kajusK/Pneumobil/fw/sources/app/hmi/state.c

/*
    BUT pneumobil - Copyright (C) 2018 Jakub Kaderka.

    This file is part of BUT pneumobil.

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
    You should have received a copy of the GNU General Public License
    along with this program.  If not, see <http://www.gnu.org/licenses/>.
*/

/**
 * @file    hmi/state.c
 * @brief   Collecting data from various modules to get car state
 *
 * @addtogroup app-hmi
 * @{
 */

#include <string.h>
#include <modules/log.h>
#include <modules/comm/comm.h>
#include <utils/time.h>
#include <utils/assert.h>

#include "logger.h"
#include "state.h"

/** Time from last module seen time to consider it online */
#define STATE_CONSIDER_ONLINE_MS 5000

static uint32_t statei_race_start_ts;
static state_t statei_state;
static state_pneu_t * const statei_pneu = &statei_state.pneu;
static state_car_t * const statei_car = &statei_state.car;
static state_psu_t * const statei_psu = &statei_state.psu;

static void Statei_SetNodeOnline(state_node_t *module)
{
    ASSERT_NOT(module == NULL);

    if ((millis() - module->_seen) > STATE_CONSIDER_ONLINE_MS) {
        module->online = false;
    } else {
        module->online = true;
    }
}

void State_UpdateCarState(uint16_t speed_dms, uint16_t speed_avg_dms,
        uint16_t distance_m, race_mode_t mode)
{
    statei_car->speed_kmh = speed_dms*0.36;
    statei_car->speed_avg_kmh = speed_avg_dms*0.36;
    statei_car->distance_m = distance_m;
    statei_car->mode = mode;

    if (statei_car->speed_kmh > statei_car->speed_max_kmh) {
        statei_car->speed_max_kmh = statei_car->speed_kmh;
    }
}

void State_UpdateCarIoState(valve_state_t front1, valve_state_t front2,
        valve_state_t back1, valve_state_t back2, bool endstop_front,
        bool endstop_back, bool throttle, bool brake, bool horn, bool shifting,
        uint8_t gear)
{
    statei_pneu->valve_front1 = front1;
    statei_pneu->valve_front2 = front2;
    statei_pneu->valve_back1 = back1;
    statei_pneu->valve_back2 = back2;
    statei_pneu->endstop_front = endstop_front;
    statei_pneu->endstop_back = endstop_back;
    statei_car->throttle = throttle;
    statei_car->brake = brake;
    statei_car->horn = horn;
    statei_car->shifting = shifting;
    statei_car->gear = gear;
}

void State_UpdatePneuState(uint16_t press1_kpa, uint16_t press2_kpa,
        uint16_t press3_kpa, uint8_t piston_pos_pct)
{
    statei_pneu->press1_kpa = press1_kpa;
    statei_pneu->press2_kpa = press2_kpa;
    statei_pneu->press3_kpa = press3_kpa;
    statei_pneu->piston_pct = piston_pos_pct;
}

void State_UpdateBattery(uint16_t bat1_mv, uint16_t bat2_mv, uint16_t cur_ma,
        uint8_t charge_pct)
{
    statei_psu->battery.bat1_mv = bat1_mv;
    statei_psu->battery.bat2_mv = bat2_mv;
    statei_psu->battery.cur_ma = cur_ma;
    statei_psu->battery.charge_pct = charge_pct;
}

void State_UpdatePSUCurrent(uint16_t cur5v_ma, uint16_t cur12v_ma,
        uint16_t cur24v_ma)
{
    statei_psu->psu5_ma = cur5v_ma;
    statei_psu->psu12_ma = cur12v_ma;
    statei_psu->psu24_ma = cur24v_ma;
}

void State_UpdatePSUVoltage(uint16_t volt5_mv, uint16_t volt12_mv,
        uint16_t volt24_mv)
{
    statei_psu->psu5_mv = volt5_mv;
    statei_psu->psu12_mv = volt12_mv;
    statei_psu->psu24_mv = volt24_mv;
}

void State_UpdateNode(comm_node_t node, uint16_t uptime_s, int8_t temp_c,
        uint16_t core_mv)
{
    state_node_t *node_var;

    switch (node) {
        case COMM_NODE_PSU:
            node_var = &statei_state.node.psu;
            break;
        case COMM_NODE_ECU:
            node_var = &statei_state.node.ecu;
            break;
        case COMM_NODE_SDU:
            node_var = &statei_state.node.sdu;
            break;
        case COMM_NODE_DEBUG:
            node_var = &statei_state.node.dbg;
            break;
        case COMM_NODE_HMI:
            Log_Error(LOG_SOURCE_APP,
                    "Received state of HMI that was not sent by HMI");
            return;
            break;
        default:
            Log_Error(LOG_SOURCE_APP, "Received state for unknown module %d",
                    node);
            return;
            break;
    }

    node_var->uptime_s = uptime_s;
    node_var->temp_c = temp_c;
    node_var->core_mv = core_mv;
    node_var->_seen = millis();
}

state_t *State_Get(void)
{
    Statei_SetNodeOnline(&statei_state.node.ecu);
    Statei_SetNodeOnline(&statei_state.node.psu);
    Statei_SetNodeOnline(&statei_state.node.sdu);
    Statei_SetNodeOnline(&statei_state.node.dbg);

    //TODO
    statei_state.node.hmi.online = true;
    statei_state.node.hmi.core_mv = 0;
    statei_state.node.hmi.temp_c = 0;
    statei_state.node.hmi.uptime_s = millis()/1000;

    return &statei_state;
}

race_mode_t State_GetRaceMode(void)
{
    return statei_state.car.mode;
}

uint32_t State_GetRaceTimeMs(void)
{
    return millis() - statei_race_start_ts;
}

bool State_SetRaceMode(race_mode_t mode)
{
    Log_Info(LOG_SOURCE_APP, "Setting race mode to %d", mode);
    statei_state.car.mode = mode;
    Logger_NewRaceLogFile();
    statei_race_start_ts = millis();
    statei_car->speed_max_kmh = 0;
    return Comm_SendEcuStartRace(mode);
}

void State_Init(void)
{
    memset(&statei_state, 0, sizeof(statei_state));
}

/** @} */
