kajusK/Pneumobil/fw/sources/app/hmi/state.h

/*
    BUT pneumobil - Copyright (C) 2018 Jakub Kaderka.

    This file is part of BUT pneumobil ECU.

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
    You should have received a copy of the GNU General Public License
    along with this program.  If not, see <http://www.gnu.org/licenses/>.
*/

/**
 * @file    hmi/state.c
 * @brief   Collecting data from various modules to get car state
 *
 * @addtogroup app-hmi
 */

#ifndef __HMI_STATE_H
#define __HMI_STATE_H

#include <types.h>
#include <car_defs.h>

typedef struct {
    uint8_t piston_pct;
    uint16_t press1_kpa;
    uint16_t press2_kpa;
    uint16_t press3_kpa;
    valve_state_t valve_front1;
    valve_state_t valve_front2;
    valve_state_t valve_back1;
    valve_state_t valve_back2;
    bool endstop_front;
    bool endstop_back;
} state_pneu_t;

typedef struct {
    float speed_kmh;
    float speed_avg_kmh;
    float speed_max_kmh;
    uint16_t distance_m;
    race_mode_t mode;
    bool throttle;
    bool brake;
    bool horn;
    bool shifting;
    uint8_t gear;
} state_car_t;

typedef struct {
    uint16_t bat1_mv;
    uint16_t bat2_mv;
    uint16_t cur_ma;
    uint8_t charge_pct;
} state_battery_t;

typedef struct {
    state_battery_t battery;
    uint16_t psu5_mv;
    uint16_t psu12_mv;
    uint16_t psu24_mv;
    uint16_t psu5_ma;
    uint16_t psu12_ma;
    uint16_t psu24_ma;
} state_psu_t;

typedef struct {
    uint32_t _seen;
    bool online;
    uint16_t core_mv;
    int8_t temp_c;
    uint16_t uptime_s;
} state_node_t;

typedef struct {
    state_node_t psu;
    state_node_t hmi;
    state_node_t ecu;
    state_node_t sdu;
    state_node_t dbg;
} state_nodes_t;

typedef struct {
    state_psu_t psu;
    state_car_t car;
    state_pneu_t pneu;
    state_nodes_t node;
} state_t;

/*
 * Setters for the internal state variables, usually called from comm module
 */
extern void State_UpdateCarState(uint16_t speed_dms, uint16_t speed_avg_dms,
        uint16_t distance_m, race_mode_t mode);
extern void State_UpdateCarIoState(valve_state_t front1, valve_state_t front2,
        valve_state_t back1, valve_state_t back2, bool endstop_front,
        bool endstop_back, bool throttle, bool brake, bool horn, bool shifting,
        uint8_t gear);
extern void State_UpdatePneuState(uint16_t press1_kpa, uint16_t press2_kpa,
        uint16_t press3_kpa, uint8_t piston_pos_pct);
extern void State_UpdateBattery(uint16_t bat1_mv, uint16_t bat2_mv,
        uint16_t cur_ma, uint8_t charge_pct);
extern void State_UpdatePSUCurrent(uint16_t cur5v_ma, uint16_t cur12v_ma,
        uint16_t cur24v_ma);
extern void State_UpdatePSUVoltage(uint16_t volt5_mv, uint16_t volt12_mv,
        uint16_t volt24_mv);

#include <modules/comm/comm.h>
extern void State_UpdateNode(comm_node_t node, uint16_t uptime_s, int8_t temp_c,
        uint16_t core_mv);

/**
 * Get car state data
 *
 * @return Pointer to internal status structure
 */
extern state_t *State_Get(void);

/**
 * Get current ECU race mode
 */
extern race_mode_t State_GetRaceMode(void);

/**
 * Get time since the last call to SetRaceMode
 *
 * @return time in milliseconds
 */
extern uint32_t State_GetRaceTimeMs(void);

/**
 * Send command to change race mode to ecu
 *
 * @param [in] mode     Mode to be used
 */
extern bool State_SetRaceMode(race_mode_t mode);

/**
 * Initialize State module
 */
extern void State_Init(void);

#endif

/** @} */
