kajusK/Pneumobil/fw/sources/app/ecu/ecu_io.c

/*
    BUT pneumobil - Copyright (C) 2018 Jakub Kaderka.

    This file is part of BUT pneumobil.

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
    You should have received a copy of the GNU General Public License
    along with this program.  If not, see <http://www.gnu.org/licenses/>.
*/

/**
 * @file    ecu_io.c
 * @brief   Processing inputs and outputs to ECU module
 *
 *TODO add config to invert pin polarity
 *
 * @addtogroup app-ecu
 * @{
 */

#include <hal.h>

#include <utils/assert.h>
#include <modules/log.h>
#include <modules/config.h>
#include <utils/buttons.h>
#include <drivers/dac.h>

#include "race.h"
#include "ecu_io.h"

static bool ECUi_GetBtThrottle(void)
{
    static bool prev = 0;
    static bt_debounce_t deb = { 0 };
    bool state;

    state = Bt_Debounce(palReadLine(LINE_BT_THROTTLE), &deb);
    if (Bt_GetEdge(state, &prev) == BT_EDGE_RISING) {
        return true;
    }
    return false;
}

static bool ECUi_GetBtMode(void)
{
    static bool prev = 0;
    static bt_debounce_t deb = { 0 };
    bool state;

    state = Bt_Debounce(!palReadLine(LINE_BT_MODE), &deb);
    if (Bt_GetEdge(state, &prev) == BT_EDGE_RISING) {
        return true;
    }
    return false;
}

static void ECUi_ValveFront1(valve_state_t state)
{
    switch (state) {
        case VALVE_CLOSED:
            palClearLine(LINE_VALVE_F1A);
            palClearLine(LINE_VALVE_F1B);
            break;
        case VALVE_IN:
            palClearLine(LINE_VALVE_F1A);
            palSetLine(LINE_VALVE_F1B);
            break;
        case VALVE_OUT:
            palSetLine(LINE_VALVE_F1A);
            palClearLine(LINE_VALVE_F1B);
            break;
    }
}

static valve_state_t ECUi_ValveFront1Get(void)
{
    bool a = palReadLine(LINE_VALVE_F1A);
    bool b = palReadLine(LINE_VALVE_F1B);

    if (a == true && b == false) {
        return VALVE_OUT;
    } else if (a == false && b == true) {
        return VALVE_IN;
    }
    return VALVE_CLOSED;
}

static void ECUi_ValveFront2(valve_state_t state)
{
    switch (state) {
        case VALVE_CLOSED:
            palClearLine(LINE_VALVE_F2A);
            palClearLine(LINE_VALVE_F2B);
            break;
        case VALVE_IN:
            palClearLine(LINE_VALVE_F2A);
            palSetLine(LINE_VALVE_F2B);
            break;
        case VALVE_OUT:
            palSetLine(LINE_VALVE_F2A);
            palClearLine(LINE_VALVE_F2B);
            break;
    }
}

static valve_state_t ECUi_ValveFront2Get(void)
{
    bool a = palReadLine(LINE_VALVE_F2A);
    bool b = palReadLine(LINE_VALVE_F2B);

    if (a == true && b == false) {
        return VALVE_OUT;
    } else if (a == false && b == true) {
        return VALVE_IN;
    }
    return VALVE_CLOSED;
}

static void ECUi_ValveBack1(valve_state_t state)
{
    switch (state) {
        case VALVE_CLOSED:
            palClearLine(LINE_VALVE_B1A);
            palClearLine(LINE_VALVE_B1B);
            break;
        case VALVE_OUT:
            palClearLine(LINE_VALVE_B1A);
            palSetLine(LINE_VALVE_B1B);
            break;
        case VALVE_IN:
            palSetLine(LINE_VALVE_B1A);
            palClearLine(LINE_VALVE_B1B);
            break;
    }
}

static valve_state_t ECUi_ValveBack1Get(void)
{
    bool a = palReadLine(LINE_VALVE_B1A);
    bool b = palReadLine(LINE_VALVE_B1B);

    if (a == true && b == false) {
        return VALVE_IN;
    } else if (a == false && b == true) {
        return VALVE_OUT;
    }
    return VALVE_CLOSED;
}

static void ECUi_ValveBack2(valve_state_t state)
{
    switch (state) {
        case VALVE_CLOSED:
            palClearLine(LINE_VALVE_B2A);
            palClearLine(LINE_VALVE_B2B);
            break;
        case VALVE_OUT:
            palClearLine(LINE_VALVE_B2A);
            palSetLine(LINE_VALVE_B2B);
            break;
        case VALVE_IN:
            palSetLine(LINE_VALVE_B2A);
            palClearLine(LINE_VALVE_B2B);
            break;
    }
}

static valve_state_t ECUi_ValveBack2Get(void)
{
    bool a = palReadLine(LINE_VALVE_B2A);
    bool b = palReadLine(LINE_VALVE_B2B);

    if (a == true && b == false) {
        return VALVE_IN;
    } else if (a == false && b == true) {
        return VALVE_OUT;
    }
    return VALVE_CLOSED;
}

void ECU_ValvesBackClose(void)
{
    ECUi_ValveBack1(VALVE_CLOSED);
    ECUi_ValveBack2(VALVE_CLOSED);
}

void ECU_ValvesFrontClose(void)
{
    ECUi_ValveFront1(VALVE_CLOSED);
    ECUi_ValveFront2(VALVE_CLOSED);
}

void ECU_ValvesClose(void)
{
    ECU_ValvesBackClose();
    ECU_ValvesFrontClose();
}

void ECU_ValvesMoveFront(bool dual)
{
    ECUi_ValveFront1(VALVE_OUT);
    ECUi_ValveFront2(VALVE_OUT);

    ECUi_ValveBack1(VALVE_IN);
    if (dual) {
        ECUi_ValveBack2(VALVE_IN);
    } else {
        ECUi_ValveBack2(VALVE_CLOSED);
    }
}

void ECU_ValvesMoveBack(bool dual)
{
    ECUi_ValveBack1(VALVE_OUT);
    ECUi_ValveBack2(VALVE_OUT);

    ECUi_ValveFront1(VALVE_IN);
    if (dual) {
        ECUi_ValveFront2(VALVE_IN);
    } else {
        ECUi_ValveFront2(VALVE_CLOSED);
    }
}

void ECU_ValvesSet(const ecu_valves_t *valves)
{
    ASSERT_NOT(valves == NULL);

    ECUi_ValveBack1(valves->back1);
    ECUi_ValveBack2(valves->back2);
    ECUi_ValveFront1(valves->front1);
    ECUi_ValveFront2(valves->front2);
}

void ECU_ValvesGet(ecu_valves_t *valves)
{
    ASSERT_NOT(valves == NULL);

    valves->back1 = ECUi_ValveBack1Get();
    valves->back2 = ECUi_ValveBack2Get();
    valves->front1 = ECUi_ValveFront1Get();
    valves->front2 = ECUi_ValveFront2Get();
}

void ECU_SetRegulatorPressure(uint32_t pressure_hpa)
{
    uint16_t voltage_mv;
    /*
     * 4mA = 0Bar, 20mA = 10Bar
     * Measuring voltage drop on sense resistor (150 ohm)
     *
     * p = 10000/16*I - 10000/4 = 625*I - 2500
     * Where p is pressure in hpa, I current in mA
     *
     * Voltage on resistor is:
     * U = RI = R * (p+2500)/625
     */
    if (pressure_hpa > 10000)
            pressure_hpa = 10000;

    voltage_mv = (ECU_RSENS_OHM * (pressure_hpa + 2500))/625;
    Dacd_SetOutputMv(voltage_mv);
}

void ECU_GetRawInputs(ecu_inputs_t *inputs)
{
    ASSERT_NOT(inputs == NULL);

    if (Config_GetBool(CONFIG_BOOL_ENCODER_INVERT)) {
        inputs->endstop_front = !palReadLine(LINE_ENDSTOP_F1);
        inputs->endstop_back = !palReadLine(LINE_ENDSTOP_B1);
    } else {
        inputs->endstop_front = palReadLine(LINE_ENDSTOP_F1);
        inputs->endstop_back = palReadLine(LINE_ENDSTOP_B1);
    }
    inputs->throttle = !palReadLine(LINE_THROTTLE);
    inputs->brake = palReadLine(LINE_BRAKE);
    inputs->shifting = palReadLine(LINE_BT_SHIFTING);
    /* TODO workaround using bt throttle */
    inputs->horn = !palReadLine(LINE_BT_THROTTLE);
}

uint8_t ECU_GetGear(void)
{
    bool gear1 = !palReadLine(LINE_GEARBOX_1);
    bool gear2 = false;
//    bool gear2 = !palReadLine(LINE_GEARBOX_2);

    if (!gear1 && !gear2) {
        return 0;
    }

    if (gear1) {
        return 1;
    }
    return 2;
}

void ECU_GetInputs(ecu_inputs_t *inputs)
{
    static bt_debounce_t deb[6] = { 0 };
    static bool prev[2] = { 0 };
    ASSERT_NOT(inputs == NULL);

    ECU_GetRawInputs(inputs);
    inputs->endstop_front = Bt_Debounce(inputs->endstop_front, &deb[0]);
    inputs->endstop_front = Bt_GetEdge(inputs->endstop_front, &prev[0]) == BT_EDGE_RISING;
    inputs->endstop_back = Bt_Debounce(inputs->endstop_back, &deb[1]);
    inputs->endstop_back = Bt_GetEdge(inputs->endstop_back, &prev[1]) == BT_EDGE_RISING;

    inputs->throttle = Bt_Debounce(inputs->throttle, &deb[2]); //| ECUi_GetBtThrottle();
    inputs->brake = Bt_Debounce(inputs->brake, &deb[3]);
    inputs->shifting = Bt_Debounce(inputs->shifting, &deb[4]);
    inputs->horn = Bt_Debounce(inputs->horn, &deb[5]);

    ECU_SetHorn(inputs->horn);
    if (ECUi_GetBtMode()) {
        Race_NextMode();
    }
}

void ECU_SetHorn(bool on)
{
    if (on) {
        palSetLineMode(LINE_BT_HORN, PAL_MODE_OUTPUT_PUSHPULL);
        palSetLine(LINE_BT_HORN);
    } else {
        palSetLineMode(LINE_BT_HORN, PAL_MODE_INPUT);
    }
}

void ECU_SetBrakeLight(bool on)
{
    if (on) {
        palSetLineMode(LINE_BRAKE, PAL_MODE_OUTPUT_PUSHPULL);
        palSetLine(LINE_BRAKE);
    } else {
        palSetLineMode(LINE_BRAKE, PAL_MODE_INPUT);
    }

}

void ECU_SetOut1(bool on)
{
    palWriteLine(LINE_OUT1, (uint8_t)on);
}

void ECU_SetOut2(bool on)
{
    palWriteLine(LINE_OUT1, (uint8_t)on);
}

void ECU_IOInit(void)
{
    Dacd_Init();
}

/** @} */
