kajusK/Pneumobil/fw/sources/modules/comm/application.c

/*
    BUT pneumobil - Copyright (C) 2019 Jakub Kaderka.

    This file is part of BUT pneumobil.

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
    You should have received a copy of the GNU General Public License
    along with this program.  If not, see <http://www.gnu.org/licenses/>.
*/

/**
 * @file    application.c
 * @brief   Communication protocol, application layer
 *
 * @addtogroup modules-comm
 * @{
 */

#include <string.h>

#include "utils/assert.h"
#include "utils/time.h"

#include "modules/log.h"
#include "modules/storage.h"
#include "modules/comm/comm.h"
#include "modules/comm/can_transport.h"
#include "modules/comm/uart_transport.h"
#include "modules/comm/session.h"
#include "modules/comm/application.h"
#include "drivers/sys.h"

#ifdef HAS_STORAGE
    #include "modules/config.h"
#endif

static void Commi_SendLogCan(const log_msg_t *log)
{
    ASSERT_NOT(log == NULL);
    Comm_SendLog(IFACE_CAN, log);
}

static void Commi_SendLogUart(const log_msg_t *log)
{
    ASSERT_NOT(log == NULL);
#ifdef HAS_COMM_UART
    Comm_SendLog(IFACE_UART, log);
#endif
}

/* ***************************************************************************
 * Application layer module local functions
 *************************************************************************** */
comm_error_t Comm_SysStatus(const comm_sys_status_t *status)
{
    ASSERT_NOT(status == NULL);
#ifndef BOARD_HMI
    (void) status;
#else
    State_UpdateNode(status->device_id, status->uptime_s, status->core_temp_c,
            status->core_voltage_mv);
#endif

    return COMM_OK;
}

comm_error_t Comm_SetLogMask(const comm_log_mask_t *payload)
{
    ASSERT_NOT(payload == NULL);

    switch (payload->interface) {
        case COMM_LOG_IFACE_CAN:
            Log_UpdateSubscription(Commi_SendLogCan, payload->severity);
            break;
        case COMM_LOG_IFACE_UART:
            Log_UpdateSubscription(Commi_SendLogUart, payload->severity);
            break;
        default:
            return COMM_ERR_INCORRECT_PARAM;
            break;
    }
    return COMM_OK;
}

comm_error_t Comm_GetLogMask(uint8_t interface, comm_log_mask_t *response)
{
    ASSERT_NOT(response == NULL);

    switch (interface) {
        case COMM_LOG_IFACE_CAN:
            Log_GetSubscription(Commi_SendLogCan, response->severity);
            break;
        case COMM_LOG_IFACE_UART:
            Log_GetSubscription(Commi_SendLogUart, response->severity);
            break;
        default:
            return COMM_ERR_INCORRECT_PARAM;
            break;
    }
    return COMM_OK;
}

comm_error_t Comm_SetConfig(const comm_config_item_t *payload)
{
    ASSERT_NOT(payload == NULL);

#ifdef HAS_STORAGE
    switch (payload->type) {
        case COMM_CONFIG_TYPE_BOOL:
            if (payload->id >= CONFIG_BOOL_COUNT) {
                return COMM_ERR_INCORRECT_PARAM;
            }
            Config_SetBool(payload->id, (bool) payload->u32);
            break;
        case COMM_CONFIG_TYPE_UINT:
            if (payload->id >= CONFIG_UINT_COUNT) {
                return COMM_ERR_INCORRECT_PARAM;
            }
            Config_SetUint(payload->id, (bool) payload->u32);
            break;
        case COMM_CONFIG_TYPE_FLOAT:
            if (payload->id >= CONFIG_FLOAT_COUNT) {
                return COMM_ERR_INCORRECT_PARAM;
            }
            Config_SetFloat(payload->id, (float) payload->u32);
            break;

        default:
            return COMM_ERR_INCORRECT_PARAM;
            break;
    }
    return COMM_OK;
#else
    return COMM_ERR_UNSUPPORTED_CMD;
#endif
}

comm_error_t Comm_GetConfig(uint8_t id, uint8_t type,
        comm_config_item_t *response)
{
    ASSERT_NOT(response == NULL);
#ifdef HAS_STORAGE
    response->id = id;
    response->type = type;

    switch (type) {
        case COMM_CONFIG_TYPE_BOOL:
            if (id >= CONFIG_BOOL_COUNT) {
                return COMM_ERR_INCORRECT_PARAM;
            }
            response->u32 = Config_GetBool(id);
            break;
        case COMM_CONFIG_TYPE_UINT:
            if (id >= CONFIG_UINT_COUNT) {
                return COMM_ERR_INCORRECT_PARAM;
            }
            response->u32 = Config_GetUint(id);
            break;
        case COMM_CONFIG_TYPE_FLOAT:
            if (id >= CONFIG_FLOAT_COUNT) {
                return COMM_ERR_INCORRECT_PARAM;
            }
            response->u32 = Config_GetFloat(id);
            break;

        default:
            return COMM_ERR_INCORRECT_PARAM;
            break;
    }
    return COMM_OK;
#else
    (void) type;
    (void) id;
    return COMM_ERR_UNSUPPORTED_CMD;
#endif
}

comm_error_t Comm_ResetConfig(uint32_t magic)
{
#ifdef HAS_STORAGE
    if (magic == 0xdeadbeef) {
        Config_Reset();
        return COMM_OK;
    }
    return COMM_ERR_INCORRECT_PARAM;
#else
    (void) magic;
    return COMM_ERR_UNSUPPORTED_CMD;
#endif
}

comm_error_t Comm_LogMessage(uint16_t len, comm_node_t node,
        const comm_log_msg_t *payload)
{
    (void) len;
#ifndef BOARD_HMI
    (void) node;
    (void) payload;
#else
    log_module_t module;
    switch (node) {
        case COMM_NODE_ECU:
            module = LOG_MODULE_ECU;
            break;
        case COMM_NODE_PSU:
            module = LOG_MODULE_PSU;
            break;
        case COMM_NODE_HMI:
            module = LOG_MODULE_HMI;
            break;
        case COMM_NODE_SDU:
            module = LOG_MODULE_SDU;
            break;
        default:
            return COMM_ERR_INCORRECT_PARAM;
            break;
    }

    Log_AddEntry(module, payload->source, payload->severity,
            (const char *) payload->message);
#endif
    return COMM_OK;
}

comm_error_t Comm_Reboot(uint32_t magic)
{
    if (magic == 0xdeadbeef) {
#ifdef HAS_STORAGE
        Storage_WriteImmediately();
#endif
        Sysd_Reboot();
        return COMM_OK;
    }
    return COMM_ERR_INCORRECT_PARAM;
}

void Comm_CarState(const comm_car_state_t *payload)
{
    ASSERT_NOT(payload == NULL);

#ifdef BOARD_HMI
    State_UpdateCarState(payload->speed_dms, payload->speed_avg_dms,
            payload->distance_m, payload->mode);
#elif defined(BOARD_SDU)
    Sdu_SetCarState(payload->speed_dms, payload->speed_avg_dms, payload->mode);
#endif
}


/* ***************************************************************************
 * HMI specific commands
 *************************************************************************** */
#ifdef BOARD_HMI
void Comm_CarIO(const comm_car_io_t *payload)
{
    ASSERT_NOT(payload == NULL);

    //TODO make sure valves are set correctly
    State_UpdateCarIoState((payload->valves >> 6) & 0x03, /* valve front 1 */
                (payload->valves >> 4) & 0x03,      /* valve front 2 */
                (payload->valves >> 2) & 0x03,      /* valve back 1 */
                payload->valves & 0x03,             /* valve back 2 */
                (payload->endstops >> 1) & 0x01,    /* endstop front */
                payload->endstops & 0x01,           /* endstop back */
                payload->inputs & 0x01,             /* throttle */
                (payload->inputs >> 1) & 0x01,      /* brake */
                (payload->inputs >> 2) & 0x01,      /* horn */
                (payload->inputs >> 3) & 0x01,      /* shifting */
                payload->gear);
}

void Comm_PneuState(const comm_pneu_state_t *payload)
{
    ASSERT_NOT(payload == NULL);

    State_UpdatePneuState(payload->press1_kpa, payload->press2_kpa,
            payload->press3_kpa, payload->piston_pct);
}

void Comm_BatteryState(const comm_battery_state_t *payload)
{
    ASSERT_NOT(payload == NULL);

    State_UpdateBattery(payload->bat1_mv, payload->bat2_mv, payload->current_ma,
            payload->charge_pct);
}

void Comm_PSUCurrent(const comm_psu_current_t *payload)
{
    ASSERT_NOT(payload == NULL);

    State_UpdatePSUCurrent(payload->current5v_ma, payload->current12v_ma,
            payload->current24v_ma);
}

void Comm_PSUVoltage(const comm_psu_voltage_t *payload)
{
    ASSERT_NOT(payload == NULL);

    State_UpdatePSUVoltage(payload->voltage5v_mv, payload->voltage12v_mv,
            payload->voltage24v_mv);
}
#endif // BOARD_HMI

/* ***************************************************************************
 * ECU specific commands
 *************************************************************************** */
#ifdef BOARD_ECU
comm_error_t Comm_StartRace(uint8_t mode)
{
    if (Race_Start(mode)) {
        return COMM_OK;
    }
    return COMM_ERR_INCORRECT_PARAM;
}

comm_error_t Comm_EcuDebug(const comm_ecu_debug_t *payload)
{
    ecu_valves_t valves;
    ASSERT_NOT(payload == NULL);

    if (Race_GetMode() != RACE_MODE_DEBUG) {
        return COMM_ERR_INCORRECT_PARAM;
    }

    valves.front1 = (payload->valves >> 6) & 0x03;
    valves.front2 = (payload->valves >> 4) & 0x03;
    valves.back1 = (payload->valves >> 2) & 0x03;
    valves.back2 = payload->valves & 0x03;
    ECU_ValvesSet(&valves);

    ECU_SetHorn(payload->outputs & 0x01);
    ECU_SetBrakeLight(payload->outputs & 0x02);
    ECU_SetOut1(payload->outputs & 0x04);
    ECU_SetOut1(payload->outputs & 0x08);

    return COMM_OK;
}

comm_error_t Comm_EcuUserIo(const comm_ecu_user_io_t *payload)
{
    ASSERT_NOT(payload == NULL);

    ECU_SetHorn(payload->horn);
    ECU_SetBrakeLight(payload->brake);
    ECU_SetOut1(payload->out1);
    ECU_SetOut2(payload->out2);

    return COMM_OK;
}

comm_error_t Comm_EcuSetPneuParams(const comm_ecu_pneu_params_t *payload)
{
    ASSERT_NOT(payload == NULL);

    switch ((race_mode_t) payload->mode) {
        case RACE_MODE_ARCADE:
            Config_SetUint(CONFIG_UINT_DEADTIME_MS_ARCADE, payload->deadtime_ms);
            Config_SetUint(CONFIG_UINT_FILLING_PCT_ARCADE, payload->filling_pct);
            break;
        case RACE_MODE_ACCELERATION:
            Config_SetUint(CONFIG_UINT_DEADTIME_MS_ACCELERATION, payload->deadtime_ms);
            Config_SetUint(CONFIG_UINT_FILLING_PCT_ACCELERATION, payload->filling_pct);
            break;
        case RACE_MODE_LONG_DISTANCE:
            Config_SetUint(CONFIG_UINT_DEADTIME_MS_LONG_DIST, payload->deadtime_ms);
            Config_SetUint(CONFIG_UINT_FILLING_PCT_LONG_DIST, payload->filling_pct);
            break;
        default:
            return COMM_ERR_INCORRECT_PARAM;
            break;
    }
    return COMM_OK;
}

comm_error_t Comm_EcuGetPneuParams(uint8_t mode, comm_ecu_pneu_params_t *response)
{
    ASSERT_NOT(response == NULL);

    response->mode = mode;
    switch ((race_mode_t) mode) {
        case RACE_MODE_ARCADE:
            response->deadtime_ms = Config_GetUint(CONFIG_UINT_DEADTIME_MS_ARCADE);
            response->filling_pct = Config_GetUint(CONFIG_UINT_FILLING_PCT_ARCADE);
            break;
        case RACE_MODE_ACCELERATION:
            response->deadtime_ms = Config_GetUint(CONFIG_UINT_DEADTIME_MS_ACCELERATION);
            response->filling_pct = Config_GetUint(CONFIG_UINT_FILLING_PCT_ACCELERATION);
            break;
        case RACE_MODE_LONG_DISTANCE:
            response->deadtime_ms = Config_GetUint(CONFIG_UINT_DEADTIME_MS_LONG_DIST);
            response->filling_pct = Config_GetUint(CONFIG_UINT_FILLING_PCT_LONG_DIST);
            break;
        default:
            return COMM_ERR_INCORRECT_PARAM;
            break;
    }
    return COMM_OK;

}

comm_error_t Comm_EcuReinit(uint32_t magic)
{
    if (magic == 0xdeadbeef) {
        Config_SetUint(CONFIG_UINT_PISTON_LEN, 0);
        return COMM_OK;
    }
    return COMM_ERR_INCORRECT_PARAM;
}

comm_error_t Comm_EcuGetPneuVars(uint16_t *piston_len)
{
    ASSERT_NOT(piston_len == 0);

    *piston_len = Config_GetUint(CONFIG_UINT_PISTON_LEN);
    return COMM_OK;
}
#endif

/* ***************************************************************************
 * Application layer module global functions
 *************************************************************************** */
#ifdef BOARD_HMI
bool Comm_SendEcuStartRace(race_mode_t mode)
{
    uint8_t dummy;
    return Comm_SendPacketCmd(COMM_NODE_ECU, COMM_CMD_START_RACE,
            (uint8_t *) &mode, 1, &dummy, 1);
}

bool Comm_SendEcuDebug(valve_state_t front1, valve_state_t front2,
        valve_state_t back1, valve_state_t back2, bool horn, bool brake,
        bool out1, bool out2)
{
    comm_ecu_debug_t debug;
    uint8_t dummy;

    debug.outputs = horn | (brake << 1) | (out1 << 2) | (out2 << 3);
    debug.valves = (front1 & 0x03) << 6;
    debug.valves |= (front2 & 0x03) << 4;
    debug.valves |= (back1 & 0x03) << 2;
    debug.valves |= (back2 & 0x03);

    return Comm_SendPacketCmd(COMM_NODE_ECU, COMM_CMD_ECU_DEBUG,
            (uint8_t *) &debug, sizeof(debug), &dummy, 1);
}

bool Comm_SendEcuUserIo(bool horn, bool brake, bool out1, bool out2)
{
    uint8_t dummy;
    comm_ecu_user_io_t io;

    io.brake = brake;
    io.horn = horn;
    io.out1 = out1;
    io.out2 = out2;

    return Comm_SendPacketCmd(COMM_NODE_ECU, COMM_CMD_ECU_USER_IO,
            (uint8_t *) &io, sizeof(io), &dummy, 1);
}

bool Comm_SendPneuParams(race_mode_t mode, uint8_t filling_pct,
        uint16_t deadtime_ms)
{
    uint8_t dummy;
    comm_ecu_pneu_params_t pneu;

    pneu.mode = mode;
    pneu.filling_pct = filling_pct;
    pneu.deadtime_ms = deadtime_ms;

    return Comm_SendPacketCmd(COMM_NODE_ECU, COMM_CMD_SET_PNEU_PARAMS,
            (uint8_t *) &pneu, sizeof(pneu), &dummy, 1);
}

bool Comm_ReadPneuParams(race_mode_t mode, uint8_t *filling_pct,
        uint16_t *deadtime_ms)
{
    comm_ecu_pneu_params_t pneu;
    bool ret;

    ASSERT_NOT(filling_pct == NULL || deadtime_ms == NULL)

    ret = Comm_SendPacketCmd(COMM_NODE_ECU, COMM_CMD_GET_PNEU_PARAMS,
            (uint8_t *) &mode, 1, (uint8_t *) &pneu, sizeof(pneu));
    if (!ret) {
        return false;
    }

    *filling_pct = pneu.filling_pct;
    *deadtime_ms = pneu.deadtime_ms;
    return true;
}

bool Comm_ReadPneuVars(uint16_t *piston_len)
{
    ASSERT_NOT(piston_len == NULL);

    return Comm_SendPacketCmd(COMM_NODE_ECU, COMM_CMD_GET_PNEU_VARS,
            NULL, 0, (uint8_t *) piston_len, sizeof(*piston_len));
}

bool Comm_SendPneuReinit(void)
{
    uint32_t magic = 0xdeadbeef;

    return Comm_SendPacketCmd(COMM_NODE_ECU, COMM_CMD_PNEU_REINIT,
            (uint8_t *) &magic, sizeof(magic), NULL, 0);
}

bool Comm_SendReboot(comm_node_t node)
{
    uint32_t magic = 0xdeadbeef;

    return Comm_SendPacketCmd(node, COMM_CMD_REBOOT,
            (uint8_t *) &magic, sizeof(magic), NULL, 0);
}
#endif

#ifdef BOARD_ECU
void Comm_SendCarState(uint16_t speed_dms, uint16_t speed_avg_dms,
        uint16_t distance_m, race_mode_t race_mode)
{
    comm_car_state_t state;

    state.speed_dms = speed_dms;
    state.speed_avg_dms = speed_avg_dms;
    state.distance_m = distance_m;
    state.mode = race_mode;

    Comm_SendPacket(COMM_CMD_CAR_STATE, (uint8_t *)&state, sizeof(state));
}

void Comm_SendCarIO(const ecu_inputs_t *inputs, const ecu_valves_t *valves,
        uint8_t gear)
{
    comm_car_io_t io;
    ASSERT_NOT(valves == NULL || inputs == NULL);

    io.valves = (valves->front1 & 0x03) << 6;
    io.valves |= (valves->front2 & 0x03) << 4;
    io.valves |= (valves->back1 & 0x03) << 2;
    io.valves |= valves->back2 & 0x03;

    io.endstops = (inputs->endstop_front & 0x01) << 1;
    io.endstops |= inputs->endstop_back & 0x01;
    io.inputs = (inputs->shifting & 0x01) << 3;
    io.inputs |= (inputs->horn & 0x01) << 2;
    io.inputs |= (inputs->brake & 0x01) << 1;
    io.inputs |= inputs->throttle & 0x01;

    io.gear = gear;

    Comm_SendPacket(COMM_CMD_CAR_IO, (uint8_t *)&io, sizeof(io));
}

void Comm_SendPneuState(uint16_t press1_kpa, uint16_t press2_kpa,
        uint16_t press3_kpa, uint8_t piston_pct)
{
    comm_pneu_state_t state;

    state.press1_kpa = press1_kpa;
    state.press2_kpa = press2_kpa;
    state.press3_kpa = press3_kpa;
    state.piston_pct = piston_pct;

    Comm_SendPacket(COMM_CMD_PNEU_STATE, (uint8_t *)&state, sizeof(state));
}
#endif

#ifdef BOARD_PSU
void Comm_SendBatteryState(uint16_t b1_mv, uint16_t b2_mv, uint16_t cur_ma,
        uint8_t charge_pct)
{
    comm_battery_state_t state;

    state.bat1_mv = b1_mv;
    state.bat2_mv = b2_mv;
    state.current_ma = cur_ma;
    state.charge_pct = charge_pct;

    Comm_SendPacket(COMM_CMD_BATTERY_STATE, (uint8_t *)&state, sizeof(state));
}

void Comm_SendPSUCurrent(uint16_t v5_ma, uint16_t v12_ma, uint16_t v24_ma)
{
    comm_psu_current_t cur;

    cur.current5v_ma = v5_ma;
    cur.current12v_ma = v12_ma;
    cur.current24v_ma = v24_ma;

    Comm_SendPacket(COMM_CMD_PSU_CURRENT, (uint8_t *)&cur, sizeof(cur));
}

void Comm_SendPSUVoltage(uint16_t v5_mv, uint16_t v12_mv, uint16_t v24_mv)
{
    comm_psu_voltage_t volt;

    volt.voltage5v_mv = v5_mv;
    volt.voltage12v_mv = v12_mv;
    volt.voltage24v_mv = v24_mv;

    Comm_SendPacket(COMM_CMD_PSU_VOLTAGE, (uint8_t *)&volt, sizeof(volt));
}
#endif

void Comm_SendSystemStatus(void)
{
    comm_sys_status_t status;

    status.device_id = COMM_MY_ID;
    status.state = 0;
    status.uptime_s = millis()/1000;
    status.core_temp_c = 0;
    status.core_voltage_mv = 0;

    Comm_SendPacket(COMM_CMD_SYSTEM_STATUS, (uint8_t *)&status, sizeof(status));
}

void Comm_Init(void)
{
    log_severity_t severity[LOG_SOURCE_COUNT];

    Comm_SessionInit();
    Comm_CanInit();
#ifdef HAS_COMM_UART
    Comm_UartInit();
#endif

    for (int i = 0; i < LOG_SOURCE_COUNT; i++) {
        severity[i] = LOG_SEVERITY_WARNING;
    }
    severity[LOG_SOURCE_SYSTEM] = LOG_SEVERITY_INFO;
    severity[LOG_SOURCE_APP] = LOG_SEVERITY_INFO;
    Log_Subscribe(Commi_SendLogCan, severity, false);

    for (int i = 0; i < LOG_SOURCE_COUNT; i++) {
        severity[i] = LOG_SEVERITY_INFO;
    }
    Log_Subscribe(Commi_SendLogUart, severity, false);
}

/** @} */
