kajusK/Pneumobil/fw/sources/modules/comm/can_transport.c

/*
    BUT pneumobil - Copyright (C) 2018 Jakub Kaderka.

    This file is part of BUT pneumobil.

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
    You should have received a copy of the GNU General Public License
    along with this program.  If not, see <http://www.gnu.org/licenses/>.
*/

/**
 * @file    can_transport.c
 * @brief   Communication protocol, transport layer of can interface
 *
 * @addtogroup modules-comm
 * @{
 */

#include <string.h>
#include <ch.h>

#include "utils/assert.h"
#include "modules/log.h"
#include "utils/crc.h"
#include "drivers/can.h"
#include "modules/comm/session.h"
#include "modules/comm/can_transport.h"

/** Max length of the can data frame in bytes */
#define CAN_DATA_LEN 8

/** Structure for holding multipart frames (mailboxes) being received */
typedef struct {
    uint16_t len;       /** Amount of bytes expected */
    uint16_t received;  /** Amount of bytes received */
    bool used;          /** This slot is being used for saving right now */
    uint8_t src_id;     /** ID of the source node */
    uint8_t seq;        /** Expected sequence number of the frame */
    uint8_t payload[COMM_MAX_PAYLOAD_LEN];
} comm_can_mbox_t;

/** Can ID format */
typedef struct {
    uint16_t priority : 2;      /** Priority of the message */
    uint16_t src : 4;           /** Identifier of source node */
    uint16_t dest : 4;          /** Identifier of destination node */
    uint16_t multipart : 1;     /** multiple part message will follow */
} comm_can_id_t;

/** Storage area for multipart messages */
static comm_can_mbox_t cani_rx_mbox[COMM_CAN_MBOX_SLOTS];

/** Mutex for sending multipart messages */
MUTEX_DECL(cani_mpart_mutex);

/**
 * Convert received sid into can id structure
 *
 * The bitfields cannont be used due to way compiler arranges them to bytes
 *
 * @param sid   SID 11 bits long (aligned to LSB)
 * @return  Converted id
 */
static comm_can_id_t Commi_SID2Struct(uint32_t sid)
{
    comm_can_id_t id;

    id.multipart = sid & 0x01;
    id.dest = (sid >> 1) & 0x0f;
    id.src = (sid >> 5) & 0x0f;
    id.priority = (sid >> 9) & 0x03;
    return id;
}

/**
 * Convert given can id into SID to be send
 *
 * @param id    Can id
 * @return SID  SID aligned to right (to LSB)
 */
static uint32_t Commi_Struct2SID(comm_can_id_t id)
{
    uint32_t sid = 0;

    sid |= id.multipart & 0x01;
    sid |= (id.dest & 0x0f) << 1;
    sid |= (id.src & 0x0f) << 5;
    sid |= (id.priority & 0x03) << 9;
    return sid;
}

/**
 * Find mailbox slot to use for storing multipart messafe from given source
 *
 * @param [in] src_id       Id of the source node
 * @param [in] first        Looking for slot for first packet of multipart message
 * @return  slot id or -1 if no usable slot found
 */
static int8_t Commi_CanFindMultipartSlot(uint8_t src_id, bool first)
{
    /* Try to find used slot with same sourse */
    for (int i = 0; i < COMM_CAN_MBOX_SLOTS; i++) {
        if (cani_rx_mbox[i].src_id == src_id && cani_rx_mbox[i].used) {
            if (first) {
                Log_Warn(LOG_SOURCE_COMM,
                        "CAN overwritting previous mailbox for src %x", src_id);
            }
            return i;
        }
    }

    if (!first) {
        Log_Debug(LOG_SOURCE_COMM,
                "Ignoring unexpected multipart CAN from src %x", src_id);
        return -1;
    }

    /* find first unused slot */
    for (int i = 0; i < COMM_CAN_MBOX_SLOTS; i++) {
        if (cani_rx_mbox[i].used == false) {
            return i;
        }
    }

    Log_Error(LOG_SOURCE_COMM,
            "No available CAN mailbox, ignoring msg from %x", src_id);
    return -1;
}

/**
 * Process a multipart CAN message
 *
 * @param [in] frame    Received CAN frame
 * @return true if processing suceeded
 */
static bool Commi_CanProcessMultipart(const CANRxFrame *frame)
{
    comm_can_id_t id;
    int8_t mboxId;
    uint8_t offset = 0;
    uint16_t bytesToCopy = 0;
    uint16_t remaining = 0;
    bool lastFrame = false;
    uint8_t crc;

    ASSERT_NOT(frame == NULL);

    id = Commi_SID2Struct(frame->SID);

    if (frame->DLC < 2) {
        Log_Warn(LOG_SOURCE_COMM,
                "CAN multipart message with no payload from %x", id.src);
        return false;
    }

    mboxId = Commi_CanFindMultipartSlot(id.src, frame->data8[0] == 0x00);
    if (mboxId < 0 || mboxId >= COMM_CAN_MBOX_SLOTS) {
        return false;
    }

    /* new message */
    if (frame->data8[0] == 0x00) {
        if (frame->data8[1] > COMM_MAX_PAYLOAD_LEN) {
            Log_Warn(LOG_SOURCE_COMM,
                "CAN multipart from %x too long (%d bytes)", id.src, frame->data8[1]);
            return false;
        }

        cani_rx_mbox[mboxId].src_id = id.src;
        cani_rx_mbox[mboxId].len = frame->data8[1];
        cani_rx_mbox[mboxId].used = true;
        cani_rx_mbox[mboxId].seq = 1;
        cani_rx_mbox[mboxId].received = 0;
        offset = 2;
    } else {
        if (cani_rx_mbox[mboxId].seq != frame->data8[0]) {
            Log_Warn(LOG_SOURCE_COMM,
                    "CAN multipart id doesn't match, src %x, got %d, expected %d",
                    id.src, frame->data8[0], cani_rx_mbox[mboxId].seq);
            cani_rx_mbox[mboxId].used = false;
            return false;
        }
        cani_rx_mbox[mboxId].seq++;

        offset = 1;
    }

    remaining = cani_rx_mbox[mboxId].len - cani_rx_mbox[mboxId].received;
    if (remaining >= frame->DLC - offset) {
        bytesToCopy = frame->DLC - offset;
    } else if (remaining == frame->DLC - offset - 1) {
        /* last byte in buffer is crc */
        bytesToCopy = frame->DLC - offset - 1;
        lastFrame = true;
    } else {
        Log_Warn(LOG_SOURCE_COMM, "CAN multipart msg is too long, cropping");
        bytesToCopy = remaining;
        lastFrame = true;
    }

    memcpy(cani_rx_mbox[mboxId].payload + cani_rx_mbox[mboxId].received,
            &frame->data8[offset], bytesToCopy);
    cani_rx_mbox[mboxId].received += bytesToCopy;

    if (!lastFrame) {
        return true;
    }

    cani_rx_mbox[mboxId].used = false;

    crc = CRC8(cani_rx_mbox[mboxId].payload, cani_rx_mbox[mboxId].len);
    if (crc != frame->data8[offset+bytesToCopy]) {
        Log_Debug(LOG_SOURCE_COMM,
                "CAN crc from %x failed, got %x, expected %x",
                id.src, crc, frame->data8[offset+bytesToCopy]);
        return false;
    }

    return Comm_HandlePayload(id.src, id.dest, cani_rx_mbox[mboxId].payload,
            cani_rx_mbox[mboxId].len, Comm_CanSend);
}

/**
 * Process frame received over CAN
 *
 * @param [in] frame    Received CAN frame
 * @return      True if processing suceeded
 */
static bool Commi_CanProcessFrame(const CANRxFrame *frame)
{
    comm_can_id_t id;

    ASSERT_NOT(frame == NULL);

    /* extended identifier, must be false, we are not using those */
    if (frame->IDE) {
        Log_Warn(LOG_SOURCE_COMM, "CAN received extended identifier");
        return false;
    }
    /* remote request are not used */
    if (frame->RTR) {
        Log_Warn(LOG_SOURCE_COMM, "CAN received remote request");
        return false;
    }

    /** No need to filter ids, this is done in hardware based on can filters */
    id = Commi_SID2Struct(frame->SID);
    if (!id.multipart) {
        return Comm_HandlePayload(id.src, id.dest, frame->data8, frame->DLC,
                Comm_CanSend);
    }

    return Commi_CanProcessMultipart(frame);
}

bool Comm_CanSend(comm_node_t dest, comm_priority_t priority,
        const uint8_t *payload, uint8_t len)
{
    uint16_t sent;
    uint8_t seq = 0;
    uint8_t offset;
    uint8_t crc;
    bool crcSent;
    bool ret = true;
    CANTxFrame frame;
    comm_can_id_t id;

    ASSERT_NOT(payload == NULL);
    if (len > COMM_MAX_PAYLOAD_LEN) {
        Log_Debug(LOG_SOURCE_COMM, "Trying to send too long CAN frame (%d)", len);
        return false;
    }
    if (len == 0) {
        Log_Debug(LOG_SOURCE_COMM, "Trying to send empty CAN frame (%d)", len);
        return false;

    }

    frame.RTR = 0;
    frame.IDE = 0;
    id.src = COMM_MY_ID;
    id.dest = dest;
    id.priority = priority;
    id.multipart = 0;
    frame.SID = Commi_Struct2SID(id);

    /* Small frame */
    if (len <= 8) {
        frame.DLC = len;
        memcpy(frame.data8, payload, len);
        return Cand_SendFrame(&frame);
    }

    /* multipart message */
    id.multipart = 1;
    frame.SID = Commi_Struct2SID(id);

    seq = 0;
    sent = 0;
    offset = 2;
    frame.data8[1] = len;
    crc = CRC8(payload, len);
    crcSent = false;

    /* Lock sending by mutex so multipart message is sent as whole */
    chMtxLock(&cani_mpart_mutex);
    while (sent <= len && crcSent != true) {
        uint8_t remaining = len - sent;
        uint8_t sublen;
        if (remaining >= (CAN_DATA_LEN - offset)) {
            sublen = CAN_DATA_LEN - offset;
            frame.DLC = sublen + offset;
        } else {
            sublen = remaining;
            frame.data8[sublen+offset] = crc;
            crcSent = true;
            frame.DLC = sublen + offset + 1;
        }
        frame.data8[0] = seq;
        memcpy(&frame.data8[offset], payload+sent, sublen);

        if (!Cand_SendFrame(&frame)) {
            ret = false;
            break;
        }
        sent += sublen;
        seq++;
        offset = 1;
    }
    chMtxUnlock(&cani_mpart_mutex);

    return ret;
}

void Comm_CanInit(void)
{
    cand_filter_t filters[2];
    comm_can_id_t id = {0};
    comm_can_id_t mask = {0};

    id.dest = COMM_MY_ID;
    mask.dest = COMM_NODE_BROADCAST;
    filters[0].id = Commi_Struct2SID(id);
    filters[0].mask = Commi_Struct2SID(mask);

    id.dest = COMM_NODE_BROADCAST;
    filters[1].id = Commi_Struct2SID(id);
    filters[1].mask = Commi_Struct2SID(mask);

    Cand_Init(COMM_CAN_BAUDRATE, filters, sizeof(filters)/sizeof(filters[0]));
    Cand_RegisterRxCb(Commi_CanProcessFrame);
}

/** @} */
