kajusK/Pneumobil/fw/sources/drivers/can.c

/*
    BUT pneumobil - Copyright (C) 2018 Jakub Kaderka.

    This file is part of BUT pneumobil.

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
    You should have received a copy of the GNU General Public License
    along with this program.  If not, see <http://www.gnu.org/licenses/>.
*/

/**
 * @file    can.c
 * @brief   Can driver
 *
 * @addtogroup drivers
 * @{
 */


#include <ch.h>
#include <hal.h>

#include "utils/assert.h"
#include "modules/log.h"
#include "drivers/can.h"

#define CAND_THREAD_PRIO   NORMALPRIO
/* Define system clock for mcus with more domains */
#ifndef STM32_PCLK
    #define STM32_PCLK STM32_PCLK1
#endif

/** The can device to be used */
#define CAND JOIN(CAND, CAN_CAN_RX)

static cand_rx_cb_t candi_rx_cb;

/** Stack and stuff for thread */
THD_WORKING_AREA(candi_thread_area, 512);

static THD_FUNCTION(Cand_Thread, arg)
{
    (void) arg;
    CANRxFrame frame;
    msg_t res;

    while (true) {
        res = canReceiveTimeout(&CAND, CAN_ANY_MAILBOX, &frame, TIME_INFINITE);
        if (res != MSG_OK) {
            continue;
        }

        if (candi_rx_cb != NULL) {
            candi_rx_cb(&frame);
        }
    }
}

bool Cand_SendFrame(const CANTxFrame *frame)
{
    msg_t res;

    ASSERT_NOT(frame == NULL);

    res = canTransmitTimeout(&CAND, CAN_ANY_MAILBOX, frame, chTimeMS2I(CAN_TIMEOUT_MS));

    if (res != MSG_OK) {
        Log_Debug(LOG_SOURCE_DRIVER, "Failed to send CAN frame");
        return false;
    }
    return true;
}

void Cand_RegisterRxCb(cand_rx_cb_t cb)
{
    candi_rx_cb = cb;
}

void Cand_Init(uint32_t baudrate, const cand_filter_t *filters, uint8_t count)
{
    static CANConfig config;
    CANFilter driver_filters[STM32_CAN_MAX_FILTERS];
    uint32_t brp;

    for (int i = 0; i < count && i < STM32_CAN_MAX_FILTERS; i++) {
        driver_filters[i].filter = i;
        driver_filters[i].mode = 0; /* mask mode */
        driver_filters[i].scale = 1; /* 32 bits mode */
        driver_filters[i].assignment = 0; /* must be 0 */
        driver_filters[i].register1 = filters[i].id << CAN_RI1R_STID_Pos;
        driver_filters[i].register2 = filters[i].mask << CAN_RI1R_STID_Pos;
    }
    canSTM32SetFilters(&CAND, STM32_CAN_MAX_FILTERS,
            count, driver_filters);

    /* Auto wakeup, auto recovery */
    config.mcr = CAN_MCR_ABOM | CAN_MCR_AWUM | CAN_MCR_TXFP;
    /*
     * bit time = tq (3 + TS[3:0] + TS[2:0]) = tq * 16
     * tq = (BRP[9:0] + 1) * APB period (1/STM32_PCLK)
     */
    brp = STM32_PCLK/baudrate/16 - 1;
    config.btr = CAN_BTR_BRP(brp) | CAN_BTR_TS1(12) | CAN_BTR_TS2(1) | CAN_BTR_SJW(1);

    canStart(&CAND, &config);
    (void) chThdCreateStatic(candi_thread_area, sizeof(candi_thread_area),
                    CAND_THREAD_PRIO, Cand_Thread, NULL);
}

/** @} */
