kajusK/Pneumobil/sw/telemetry/packing.py

#!/usr/bin/python3
#
# Packing and unpacking data of various types
#

import struct

def pack_uint8(data):
    return [data & 0xff]

def pack_uint16(data):
    return [ord(c) for c in struct.pack('<H', data)]

def pack_uint32(data):
    return [ord(c) for c in struct.pack('<I', data)]

def unpack_uint8(data):
    return data

def unpack_uint16(data):
    return struct.unpack('<H',  bytes(data))[0]

def unpack_uint32(data):
    return struct.unpack('<I',  bytes(data))[0]
