kajusK/Pneumobil/fw/sources/app/hmi/gui/tabs.c

/*
    BUT pneumobil - Copyright (C) 2019 Jakub Kaderka.

    This file is part of BUT pneumobil.

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
    You should have received a copy of the GNU General Public License
    along with this program.  If not, see <http://www.gnu.org/licenses/>.
*/

/**
 * @file    hmi/gui/tabs.c
 * @brief   Drawing GUI tabs in main window
 *
 * @addtogroup gui
 * @{
 */

#include <gfx.h>
#include <chprintf.h>

#include "state.h"
#include "gui/gui.h"
#include "gui/race.h"
#include "gui/status.h"
#include "gui/setup.h"
#include "gui/debug.h"
#include "gui/console.h"

#include "gui/tabs.h"

#define BUFSIZE 64

static GHandle ghTabset;
static GHandle ghTabRace, ghTabStatus, ghTabSetup, ghTabDebug, ghTabConsole;
static GHandle ghLabelBattery;

void Gui_TabsInit(void)
{
    GWidgetInit wi;
    font_t font;

    gwinWidgetClearInit(&wi);
    wi.g.show = gTrue;
    wi.g.width = gdispGetWidth();
    wi.g.height = gdispGetHeight();
    wi.g.x = 0;
    wi.g.y = 0;

    ghTabset = gwinTabsetCreate(0, &wi, 0);
    ghTabRace = gwinTabsetAddTab(ghTabset, "Race", FALSE);
    ghTabStatus = gwinTabsetAddTab(ghTabset, "Status", FALSE);
    ghTabSetup = gwinTabsetAddTab(ghTabset, "Setup", FALSE);
    ghTabDebug = gwinTabsetAddTab(ghTabset, "Debug", FALSE);
    ghTabConsole = gwinTabsetAddTab(ghTabset, "Console", FALSE);

    Gui_RaceInit(ghTabRace);
    Gui_StatusInit(ghTabStatus);
    Gui_SetupInit(ghTabSetup);
    Gui_DebugInit(ghTabDebug);
    Gui_ConsoleInit(ghTabConsole);

    font = gwinGetDefaultFont();
    wi.g.height = gdispGetFontMetric(font, fontHeight);
    wi.g.width = gdispGetStringWidth("0000 mA 0000 mV 000%", font);
    wi.g.y = GUI_OFFSET_SPACING;
    wi.g.x = gdispGetWidth() - wi.g.width;
    wi.text = "   0 mA    0 mV   0%";
    ghLabelBattery = gwinLabelCreate(0, &wi);
}

gui_tab_t Gui_TabsGetActive(void)
{
    if (gwinGetVisible(ghTabRace)) {
        return TAB_RACE;
    }
    if (gwinGetVisible(ghTabStatus)) {
        return TAB_STATUS;
    }
    if (gwinGetVisible(ghTabSetup)) {
        return TAB_SETUP;
    }
    if (gwinGetVisible(ghTabDebug)) {
        return TAB_DEBUG;
    }
    if (gwinGetVisible(ghTabConsole)) {
        return TAB_CONSOLE;
    }

    return TAB_UNKNOWN;
}

bool Gui_TabsUpdate(void)
{
    state_t *state;
    char buf[BUFSIZE];
    state = State_Get();

    switch (Gui_TabsGetActive()) {
        case TAB_RACE:
            Gui_RaceUpdate();
            break;
        case TAB_STATUS:
            Gui_StatusUpdate();
            break;
        case TAB_SETUP:
            Gui_SetupUpdate();
            break;
        case TAB_DEBUG:
            Gui_DebugUpdate();
            break;
        case TAB_CONSOLE:
            Gui_ConsoleUpdate();
            break;
        default:
            return false;
            break;
    }

    chsnprintf(buf, BUFSIZE, "%4d mA %4d mV %3d%%", state->psu.battery.cur_ma,
            state->psu.battery.bat2_mv, state->psu.battery.charge_pct);
    Gui_LabelUpdate(ghLabelBattery, buf);

    return true;
}

bool Gui_TabsProcessEvent(GEvent *ev)
{
    if (ev->type == GEVENT_GWIN_TABSET) {
        switch (Gui_TabsGetActive()) {
            case TAB_RACE:
                Gui_RaceOnSelect();
                break;
            case TAB_SETUP:
                Gui_SetupOnSelect();
                break;
            case TAB_STATUS:
                Gui_StatusOnSelect();
                break;
            case TAB_DEBUG:
                Gui_DebugOnSelect();
                break;
            case TAB_CONSOLE:
                Gui_ConsoleOnSelect();
                break;
            default:
                break;
        }
        /* On tab change, battery label is moved to background by redraw */
        gwinRaise(ghLabelBattery);
        return true;
    }

    switch (Gui_TabsGetActive()) {
        case TAB_RACE:
            return Gui_RaceProcessEvent(ev);
        case TAB_STATUS:
            return Gui_StatusProcessEvent(ev);
        case TAB_SETUP:
            return Gui_SetupProcessEvent(ev);
        case TAB_DEBUG:
            return Gui_DebugProcessEvent(ev);
        case TAB_CONSOLE:
            return Gui_ConsoleProcessEvent(ev);
        default:
            return false;
    }
}

/** @} */
