kajusK/Pneumobil/fw/sources/tests/unit/modules/comm/test_uart_transport.c

/*
    BUT pneumobil - Copyright (C) 2018 Jakub Kaderka.

    This file is part of BUT pneumobil.

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
    You should have received a copy of the GNU General Public License
    along with this program.  If not, see <http://www.gnu.org/licenses/>.
*/

/**
 * @file    test_uart_transport.c
 * @brief   Unit test for communication module, uart transport layer
 *
 * @addtogroup tests
 * @{
 */

#include <string.h>

#include <main.h>
#include "modules/comm/uart_transport.c"

static uint8_t recbuf[30];
static uint8_t received = 0;
static bool payload_handled = false;

/* *****************************************************************************
 * Mocks
***************************************************************************** */
static bool Comm_HandlePayload(comm_node_t src, comm_node_t dest,
        const uint8_t *payload, uint8_t len, comm_send_cb_t send_frame)
{
    memcpy(recbuf, payload, len);
    received = len;
    payload_handled = true;

    TEST_ASSERT_EQUAL(COMM_NODE_DEBUG, src);
    TEST_ASSERT_EQUAL(COMM_MY_ID, dest);
    TEST_ASSERT_EQUAL_PTR(send_frame, Comm_UartSend);
    return true;
}

static void Uartd_RegisterRxCb(uartd_rx_cb_t cb)
{
    (void) cb;
}

static void Uartd_SendByte(uint8_t byte)
{
    recbuf[received++] = byte;
}

static void Uartd_Init(uint32_t baudrate)
{
    (void) baudrate;
}

static void Log_Debug(log_src_t src, const char *format, ...)
{
    (void) src;
    (void) format;
}

static void Log_Warn(log_src_t src, const char *format, ...)
{
    (void) src;
    (void) format;
}

static uint8_t CRC8_Add(uint8_t buf, uint8_t crc)
{
    (void) buf;
    (void) crc;

    return 0xab;
}

/* *****************************************************************************
 * Tests
***************************************************************************** */
TEST_GROUP(Comm_UartTransport);

TEST_SETUP(Comm_UartTransport)
{
    received = 0;
    payload_handled = false;
    memset(recbuf, 0x00, 1024);
}

TEST_TEAR_DOWN(Comm_UartTransport)
{

}

TEST(Comm_UartTransport, ProcessByteValid)
{
    /* Incorrect bytes */
    Commi_UartProcessByte(0x12);
    TEST_ASSERT_FALSE(payload_handled);
    Commi_UartProcessByte(0x19);
    TEST_ASSERT_FALSE(payload_handled);

    /* Correct payload */
    Commi_UartProcessByte(0xff);
    TEST_ASSERT_FALSE(payload_handled);
    Commi_UartProcessByte(0x12);
    TEST_ASSERT_FALSE(payload_handled);

    for (int i = 0; i < 18; i++) {
        Commi_UartProcessByte(i);
        TEST_ASSERT_FALSE(payload_handled);
    }

    /* crc */
    Commi_UartProcessByte(0xab);
    TEST_ASSERT_TRUE(payload_handled);
    TEST_ASSERT_EQUAL(18, received);

    for (int i = 0; i < 18; i++) {
        TEST_ASSERT_EQUAL_HEX8(i, recbuf[i]);
    }
}

TEST(Comm_UartTransport, ProcessByteInvalid)
{
    Commi_UartProcessByte(0xff);
    TEST_ASSERT_FALSE(payload_handled);
    Commi_UartProcessByte(0x02);
    TEST_ASSERT_FALSE(payload_handled);

    Commi_UartProcessByte(0xab);
    TEST_ASSERT_FALSE(payload_handled);
    Commi_UartProcessByte(0xcd);
    TEST_ASSERT_FALSE(payload_handled);

    /* invalid crc */
    Commi_UartProcessByte(0xcd);
    TEST_ASSERT_FALSE(payload_handled);
}

TEST(Comm_UartTransport, SendPayload)
{
    uint8_t payload[18];
    for (int i = 0; i < 18; i++) {
        payload[i] = i;
    }

    TEST_ASSERT_TRUE(Comm_UartSend(0,0, payload, 18));
    TEST_ASSERT_EQUAL(21, received);
    TEST_ASSERT_EQUAL_HEX8(0xff, recbuf[0]);
    TEST_ASSERT_EQUAL(18, recbuf[1]);
    for (int i = 0; i < 18; i++) {
        TEST_ASSERT_EQUAL_HEX8(i, recbuf[i+2]);
    }
    TEST_ASSERT_EQUAL(0xab, recbuf[20]);
}

TEST_GROUP_RUNNER(Comm_UartTransport)
{
    RUN_TEST_CASE(Comm_UartTransport, ProcessByteValid);
    RUN_TEST_CASE(Comm_UartTransport, ProcessByteInvalid);
    RUN_TEST_CASE(Comm_UartTransport, SendPayload);
}

void Comm_UartTransport_RunTests(void)
{
    RUN_TEST_GROUP(Comm_UartTransport);
}

/** @} */
